leonardsp/ESP32-Stepper-DMX-board/src/motor_dmx/pinConfig.h

#define Fan_1       27
#define Fan_2       2
#define Switch_1    35
#define Switch_2    34

#define M2_Step     18
#define M2_Dir      19

#define M1_Step    4
#define M1_Dir     5

#define StepperEnable       22

#define DimmerPin0  32
#define DimmerPin1  33
#define DimmerPin2  25
#define DimmerPin3  26
#define LEDPin      23

//Max485 on Serial1
#define Max485_TR   21
