leonardsp/ESP32-Stepper-DMX-board/src/rdm_test/pinConfig.h

#define Fan_1       27
#define Fan_2       2
#define Switch_1    35 // not used in led dimmer 
#define Switch_2    34 // not used in led dimmer

#define DimmerPin0  19
#define DimmerPin1  18

#define DimmerPin2   5
#define DimmerPin3   4

#define StepperEnable       22 // not used in led dimmer

#define DimmerPin4  32
#define DimmerPin5  33
#define DimmerPin6  25
#define DimmerPin7  26

#define LEDPin      23

//Max485 on Serial1
#define Max485_TR   21
